vives-project-xp/GreenhouseEnergy/Design/voorstellen_brandveiligheid/OnderwaterzetConcepten.png

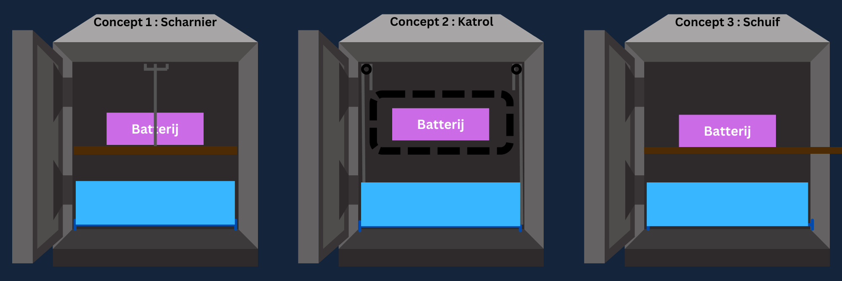
Design/voorstellen_brandveiligheid/OnderwaterzetConcepten.png
