vives-project-xp/GreenhouseEnergy/Documentation/Archief/Architectuur document.png

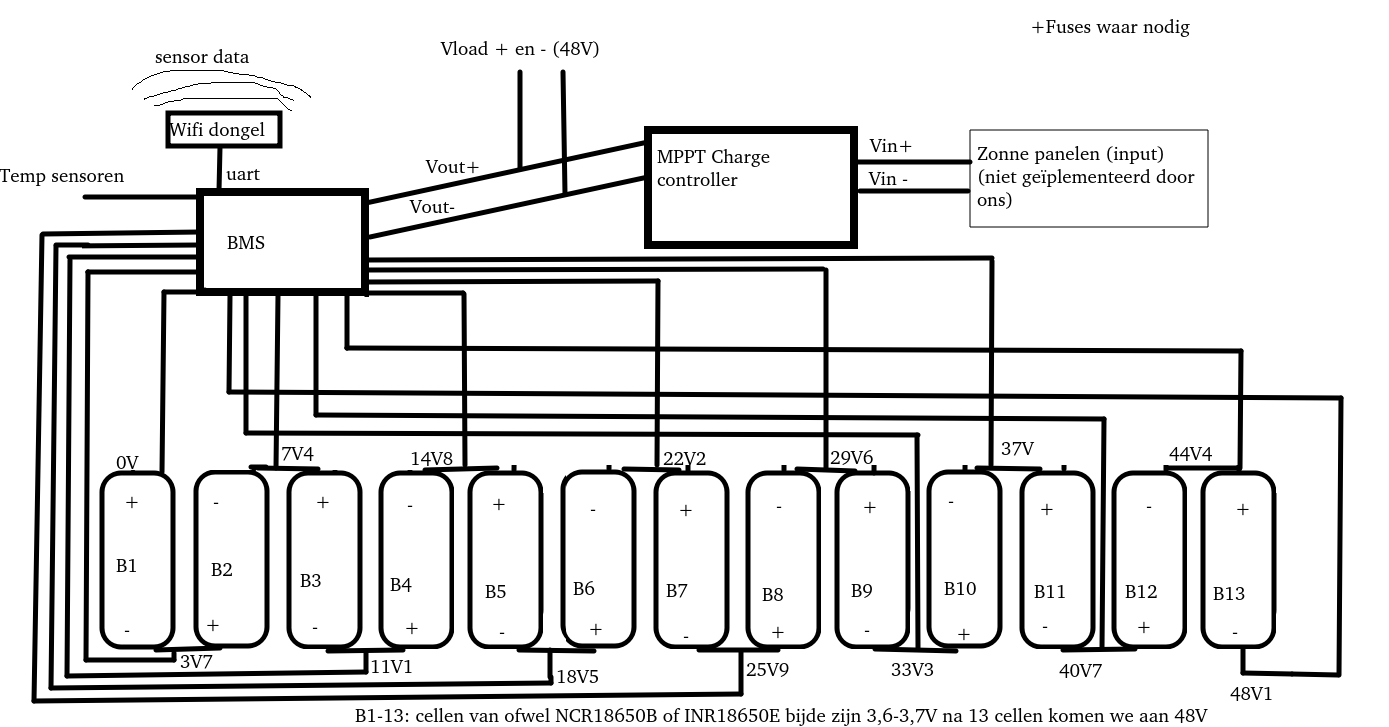
Documentation/Archief/Architectuur document.png
