vives-project-xp/GreenhouseEnergy/Documentation/Archief/Fuse schema.png

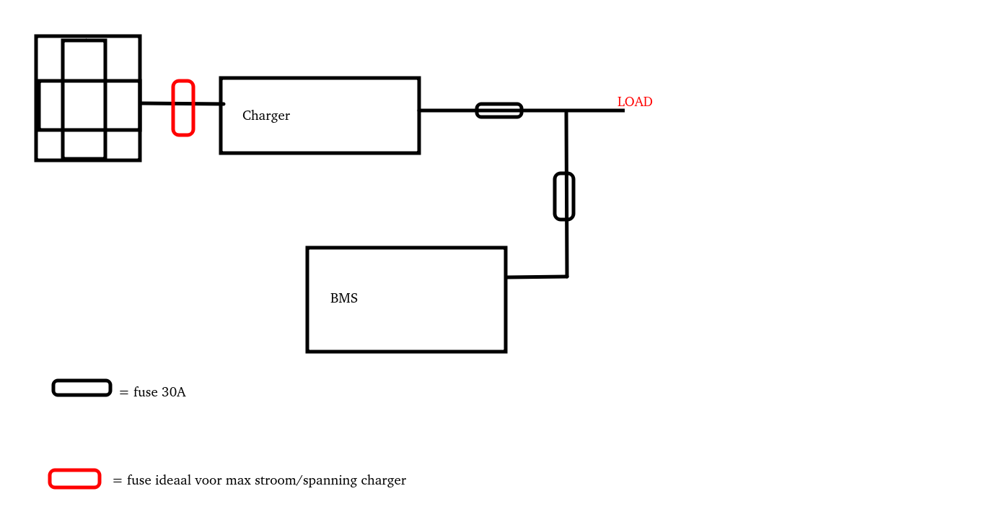
Documentation/Archief/Fuse schema.png
