vives-project-xp/GreenhouseEnergy/Documentation/Archief/K Series Smart BMS 3S to 24S 40A 60A 100A.jpg

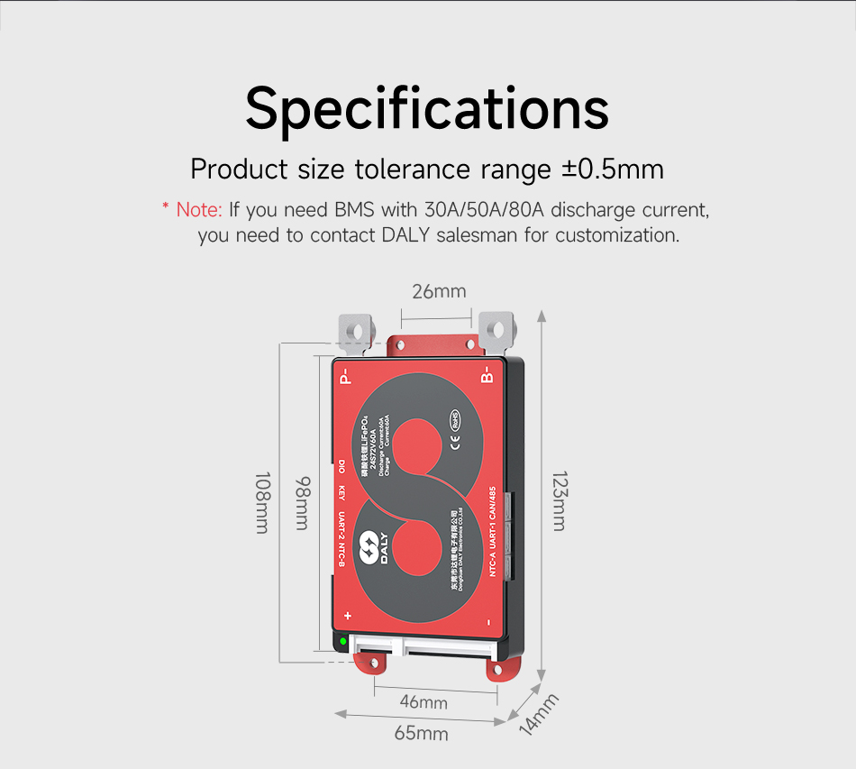
Documentation/Archief/K Series Smart BMS 3S to 24S 40A 60A 100A.jpg
