vives-project-xp/GreenhouseEnergy/Documentation/Picture Progress/Capaciteitstest van Prototype.jpg

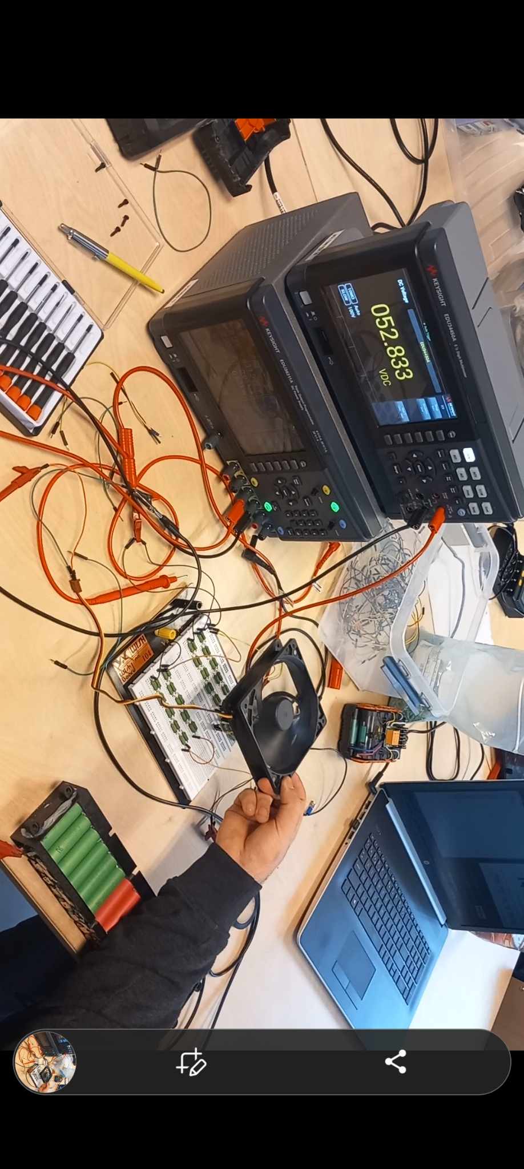
Documentation/Picture Progress/Capaciteitstest van Prototype.jpg
