vives-project-xp/GreenhouseEnergy/Documentation/Picture Progress/Ontmantelen met waterton.jpg

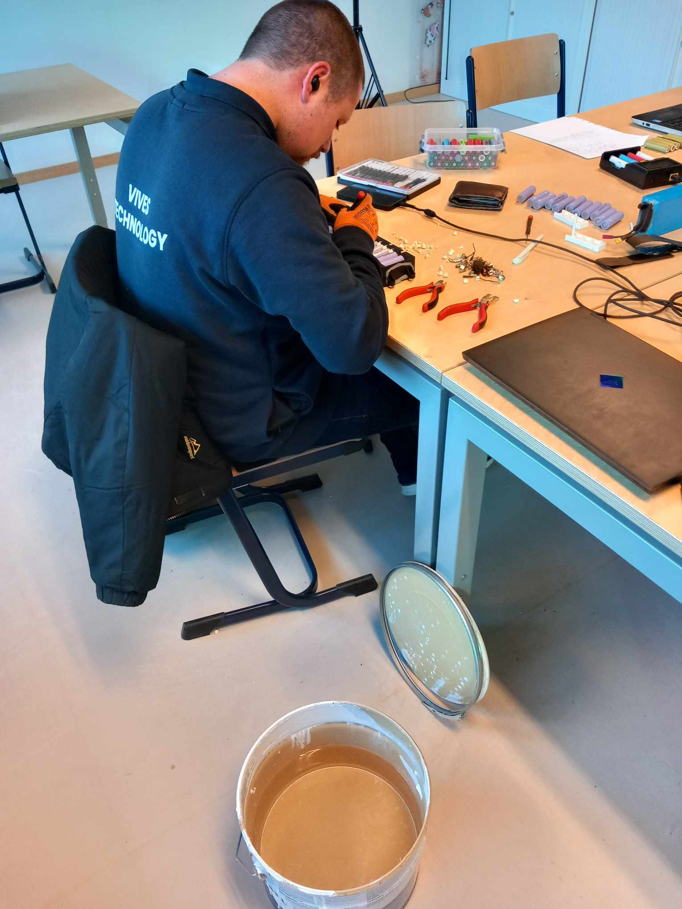
Documentation/Picture Progress/Ontmantelen met waterton.jpg
