vives-project-xp/GreenhouseEnergy/Documentation/Picture Progress/Ontmantelen van Battery packs.jpg

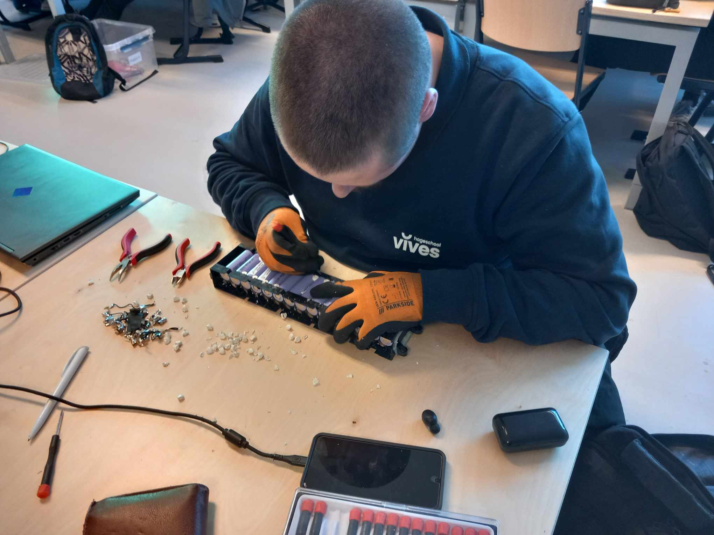
Documentation/Picture Progress/Ontmantelen van Battery packs.jpg
