vives-project-xp/GreenhouseEnergy/Documentation/Picture Progress/Prototypes.jpg

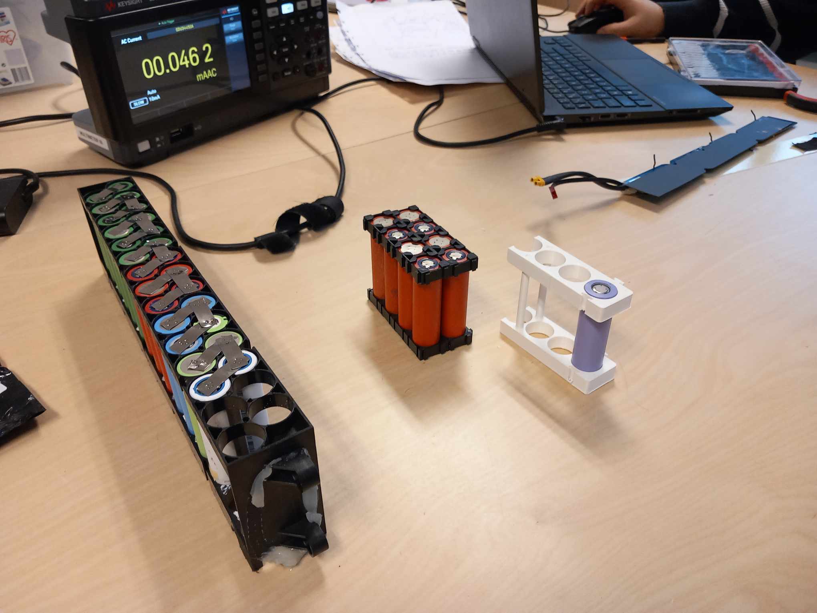
Documentation/Picture Progress/Prototypes.jpg
