vives-project-xp/GreenhouseEnergy/Documentation/Picture Progress/Puntlassen van prototype.jpg

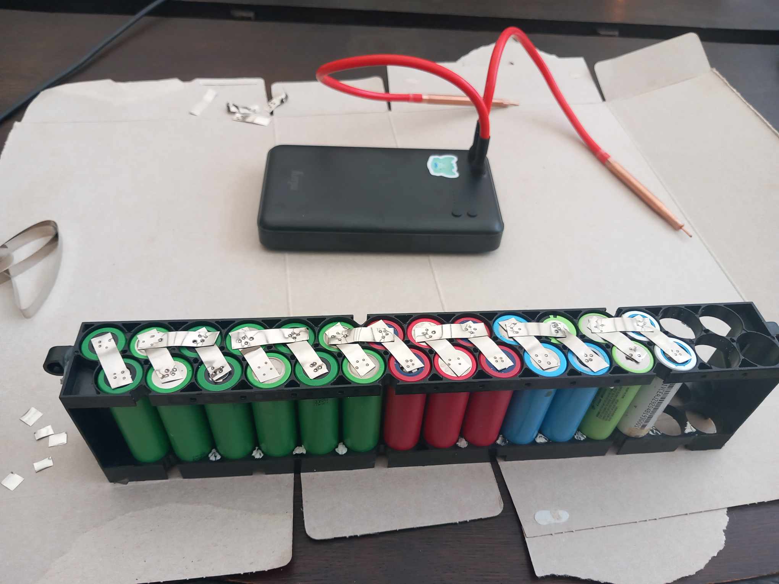
Documentation/Picture Progress/Puntlassen van prototype.jpg
