vives-project-xp/GreenhouseEnergy/Documentation/Schematics/Batterij Schematic.png

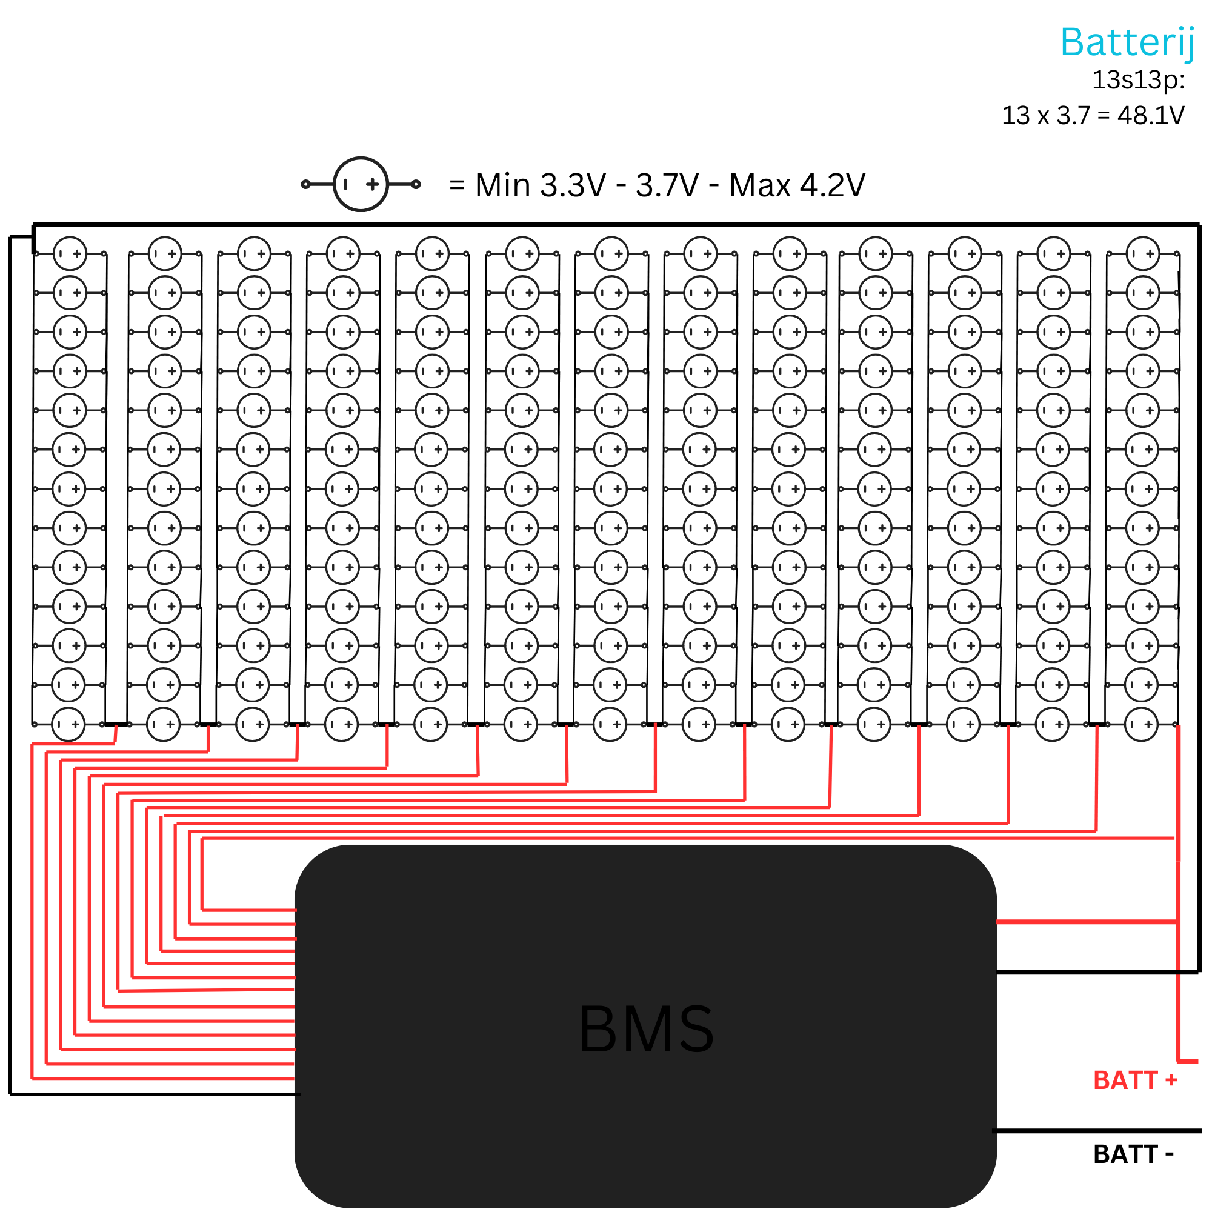
Documentation/Schematics/Batterij Schematic.png
