vives-project-xp/GreenhouseEnergy/Documentation/Schematics/Batterij TOP view.png

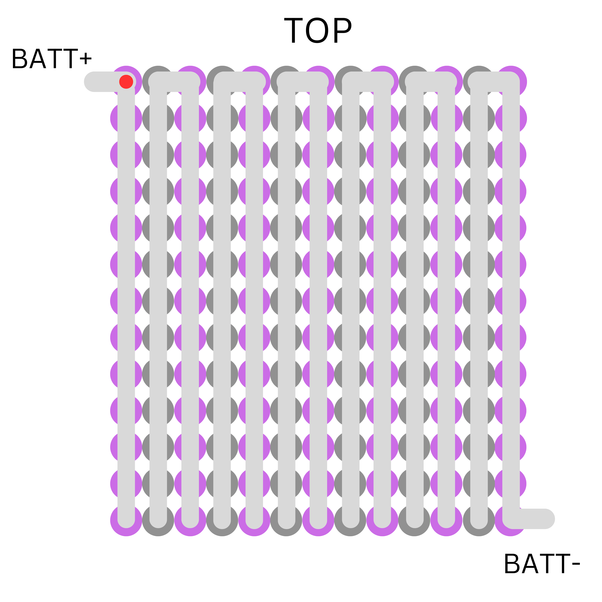
Documentation/Schematics/Batterij TOP view.png
