vives-project-xp/GreenhouseEnergy/Documentation/Schematics/Capaciteitstest Prototype (1).png

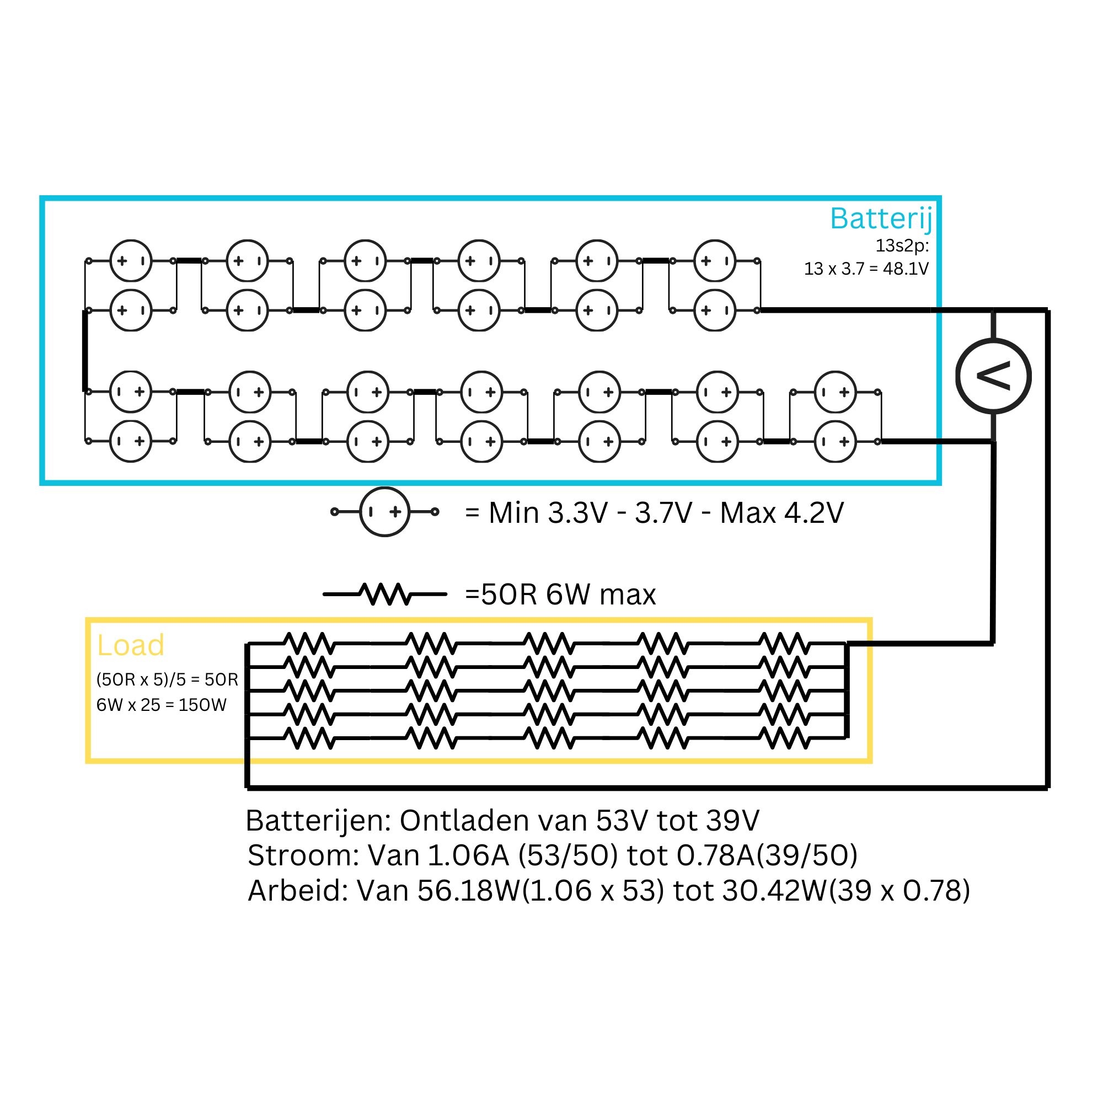
Documentation/Schematics/Capaciteitstest Prototype (1).png
