vives-project-xp/GreenhouseEnergy/Tests/Prototype/Capaciteitstest/Resultaat CapaciteitsTest.png

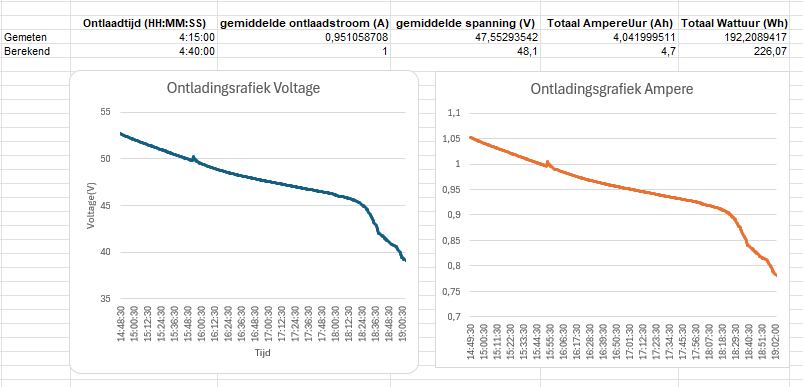
Tests/Prototype/Capaciteitstest/Resultaat CapaciteitsTest.png
